DERTECH-CORP/Velocista_COYOTE/hardware_3D/Impresion/Suplemento_motor.STL

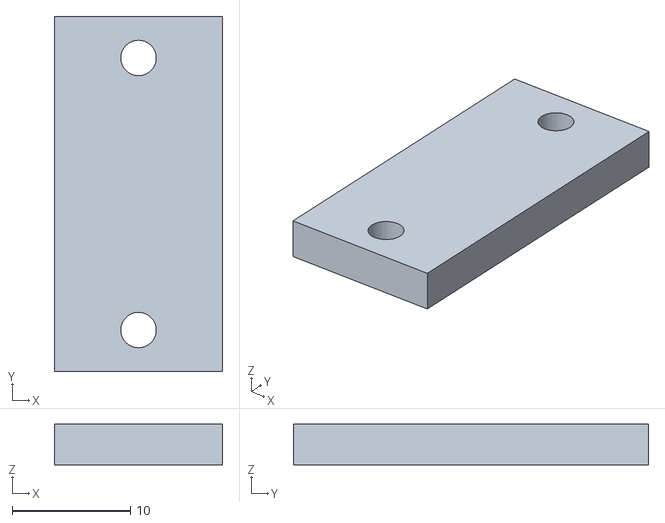
[picture p12: CAD file, 2023-10-11]
hardware_3D/Impresion/Suplemento_motor.STL
14.2 x 30.0 x 3.43
