DERTECH-CORP/Velocista_COYOTE/hardware_3D/MicroMotor_2000RPM.SLDPRT

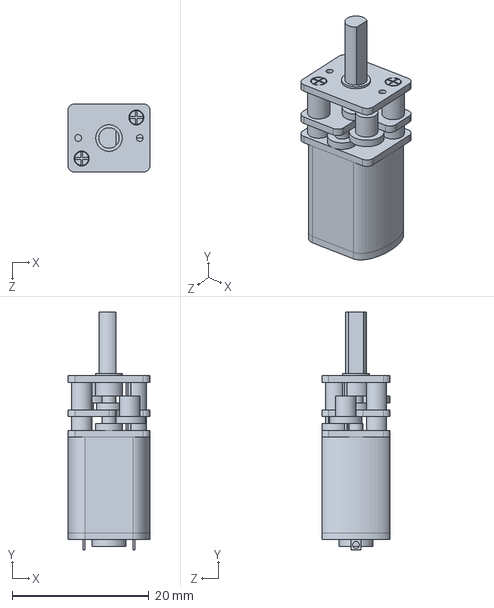
[picture p13: CAD file, 2023-10-11]
hardware_3D/MicroMotor_2000RPM.SLDPRT
12.0 x 34.8 x 10.0 mm
