DERTECH-CORP/Velocista_COYOTE/hardware_3D/Impresion/Sop_VarillaIT.STL

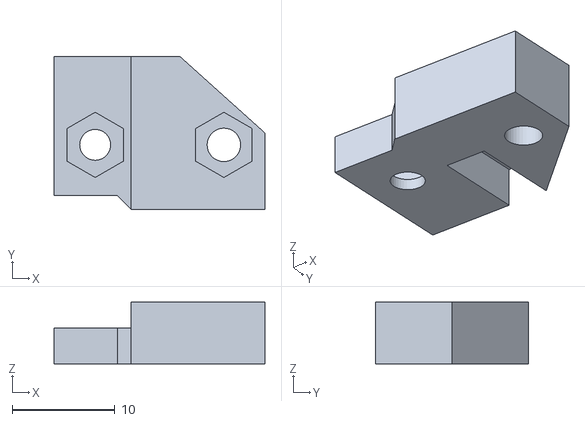
[picture p14: CAD file, 2023-10-11]
hardware_3D/Impresion/Sop_VarillaIT.STL
20.5 x 14.8 x 6.00
