DERTECH-CORP/Velocista_COYOTE/hardware_3D/Impresion/Llanta_coyote.STL

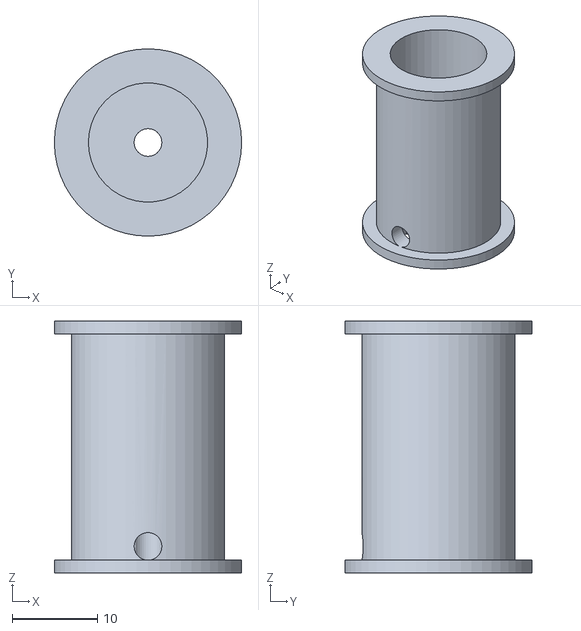
[picture p15: CAD file, 2023-10-11]
hardware_3D/Impresion/Llanta_coyote.STL
22.0 x 22.0 x 29.6
